techmannih/museview-v1/imports/TLV62569DBVR/TLV62569DBVR.step

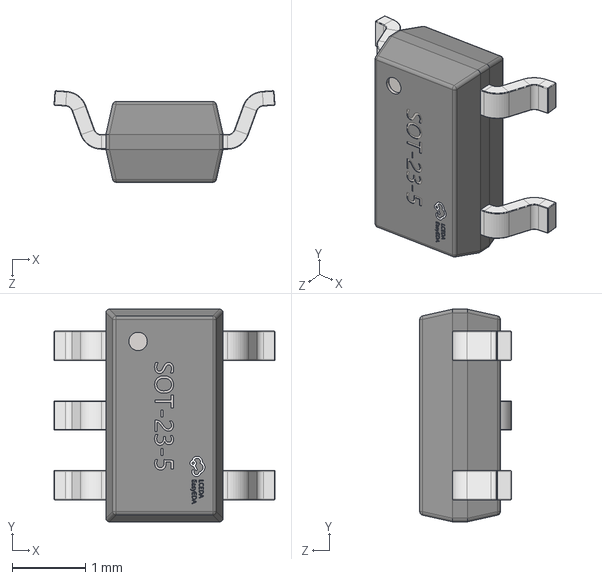
[picture p17: CAD file, 2026-10-04]
imports/TLV62569DBVR/TLV62569DBVR.step
3.01 x 2.90 x 1.25 mm
